Jbruslind/ECE341_Blue-1-/Junior Design Documentation/Review Presentation/Presentation Questions.docx

Presentation Questions

1. There are many options in regards to microcontrollers. What microcontrollers would perform best for low cost, bluetooth applications?
2. What are some options for electrical insulation for a product using 120V AC 60Hz power?
3. What are some common capabilities of “Smart” plugs?
