Jbruslind/ECE341_Blue-1-/Block Diagram/ECE341_Blue1_Block_Diagrams.docx

outside_to_system_acpwr

► system_to_outside_acpwr

Remote Switch

outside_to_system_usrin

► system_to_outside_usrout

outside_to_system_acpwr Fuse fused_acpwr Voltage

sensor_to_mcu_asig Sensor

mcu_dcpwr

sensor_to_mcu_dsig_1

system_to_outside_acpwr_1

ESP32

Block Owner

Smartphone App

Zach

Transformer

Voltage Sensor

Mack

Transformer

Jorian

ESP32

Mack

Fuse

Zach

Node

Jorian

²

_rwpcd_edonNode

Node

system_to_outside_acpwr_2

mcu_to_node_dsig_1

node_dcpwr_1

sensor_to_mcu_dsig_2

user_bluetooth_in

user_bluetooth_out

Smartphone App

user_wifi_out

²

_gisd_edon_ot_ucmuser_wifi_in

system_to_outside_usrout

outside_to_system_usrin

system_to_outside_ACpwr

sensor_to_mcu_ds

Node_dcpwr

Node "n"

C-13 AC

Plug

sensor_to_plug_fused_acpwr

mcu_to_node_dsig

relay_to_sensor_fused_acpwr

Power Relay

Current Sensor

fuse_acpwr

Interface Definitions

Interface Properties

outside_to_sytem_acpwr ● Vnominal: 120VAC via a NEMA 5-15R connector

● Ipeak: 15A

● Inominal: 500mA

fused_acpwr ● Vnominal: 120VAC via a NEMA 5-15R connector

● Ipeak: 5A

● Inominal: 500mA

● Disconnects system from input when 5A draw is exceeded

mcu_dcpwr ● Vnominal: 5VDC

● Inominal: 500mA

● Powers ESP32 Microcontroller

node_dcpwr_(n)* ● Vnominal: 5VDC

● Inominal: 500mA

● Powers Realys

sensor_to_mcu_dsig_(n)* ● Vnominal: <1VDC

● Reports current on output channels

● Inominal: <5A

mcu_to_node_dsig_(n)* ● Disables output after a time of upto 1 hour ± 1 minute when enabled

● Operate output channels independently

● Imax: 1.2A

user_bluetooth_in ● Enable/disable each channel

● Set delay on each output

● Interface must be via a mobile phone (Android)

user_bluetooth_out ● Display status of outputs

● Able to update output statuses from 20 feet away

user_wifi_in ● User interacts with system via Smartphone App

● Enable/disable each channel

● Set timer on each output

user_wifi_out ● Display status of outputs

● Able to update output statuses from 20 feet away

● Confirms length of timers

system_to_outside_usrout ● Display status of outputs

● Able to update output statuses from 20 feet away

● Confirms timers if set

outside _to_system_usrin ● User interacts with system via Smartphone App

● 9/10 users able to operate switches in <10 seconds without any previous training or knowledge of the interface

● Enable/Disable each channel

● Set delay on each output

● Accepts inputs from 20 feet away

● Disables output after a time of upto 1 hour ± 1 minute when enabled

system_to_outside_acpwr_(n)* ● Turn off and on at least 2 independent household lamps with up to 100W

incandescent bulbs and report current watts delivered by each channel

● Vnominal: 120VAC via a NEMA 5-15R connector

● Ipeak: 5A

● Inominal: 500mA

● Outputs will turn off after times of up to 60 minutes when selected

*note: n represents the nth redundant node
