Jbruslind/ECE341_Blue-1-/Final System Checkoff Documentation/Signature_Page.pdf

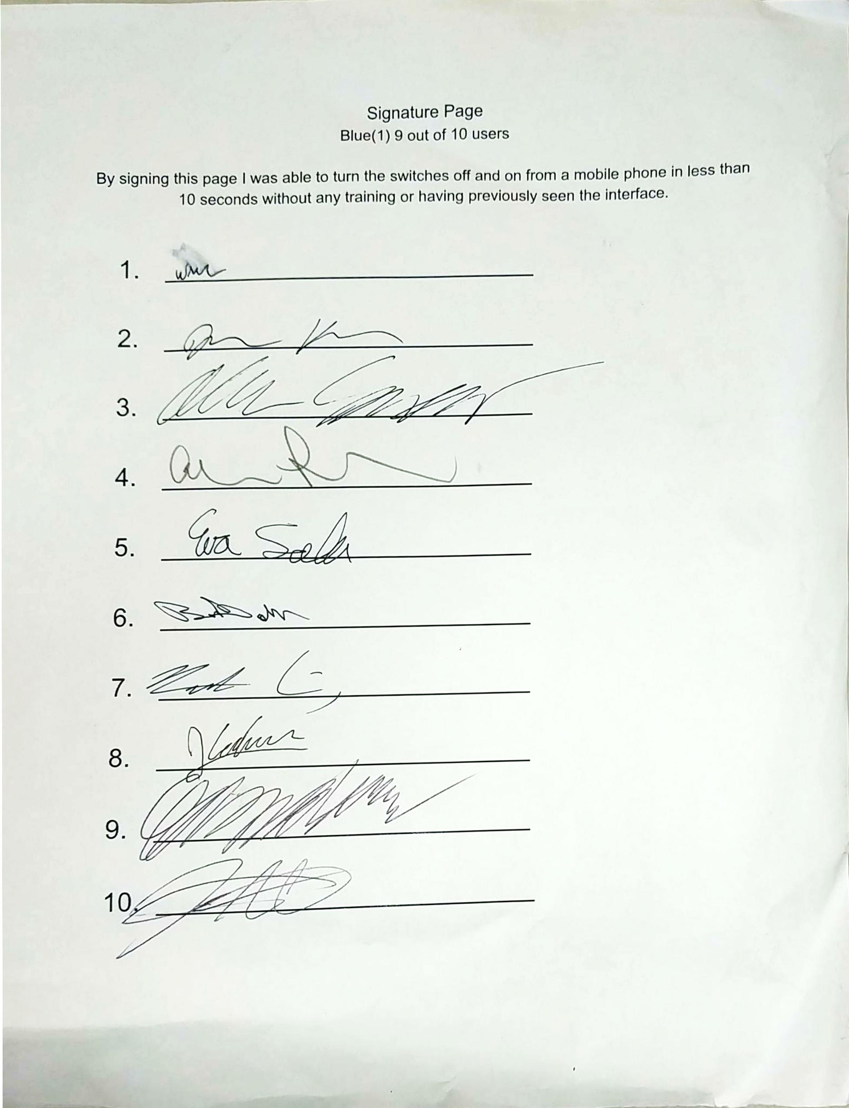
[picture p64: page 1]
