Jbruslind/ECE341_Blue-1-/Final System Checkoff Documentation/Black_Box.pdf

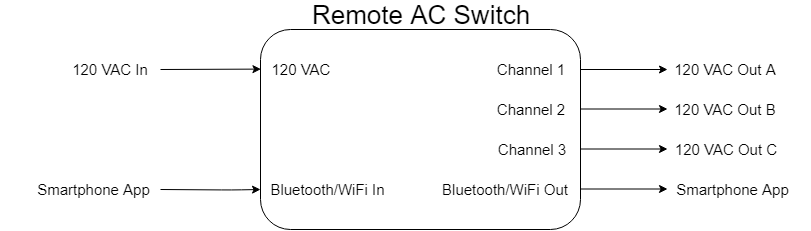
[picture p65: page 1]
