Jbruslind/ECE341_Blue-1-/Block Diagram/Old Versions/BlackBox.pdf

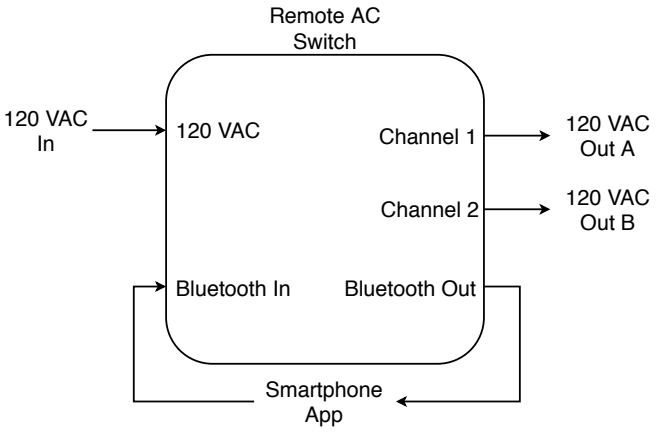
[picture p66: figure]
Remote AC Switch; 120 VAC In; 120 VAC Out A; Smartphone App; Channel 1; Channel 2; Bluetooth In; Bluetooth Out; 120 VAC; 120 VAC Out B
