Jbruslind/ECE341_Blue-1-/Block Diagram/Node_Internal.png

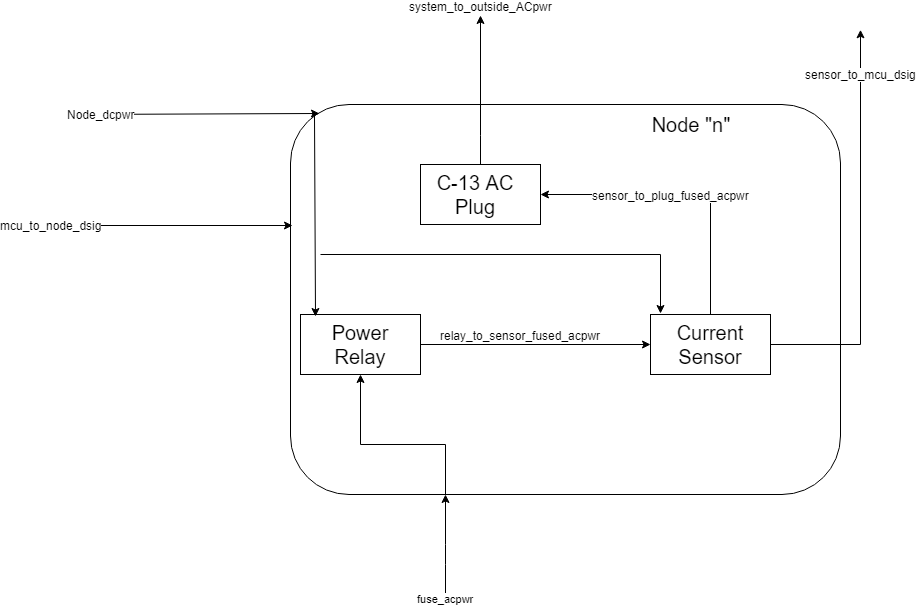
Block Diagram/Node_Internal.png
