Jbruslind/ECE341_Blue-1-/Junior Design Documentation/Poster/App Screen Shot.JPG

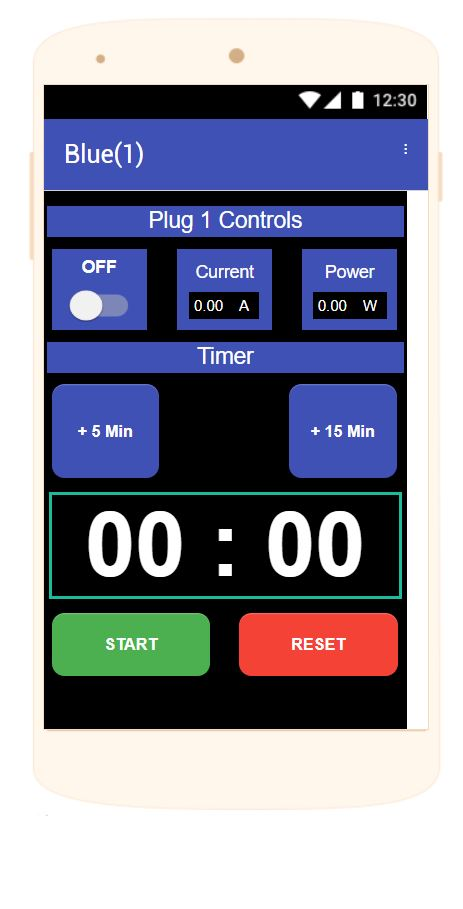
Junior Design Documentation/Poster/App Screen Shot.JPG
