Jbruslind/ECE341_Blue-1-/Junior Design Documentation/Poster/Team_photo.jpg

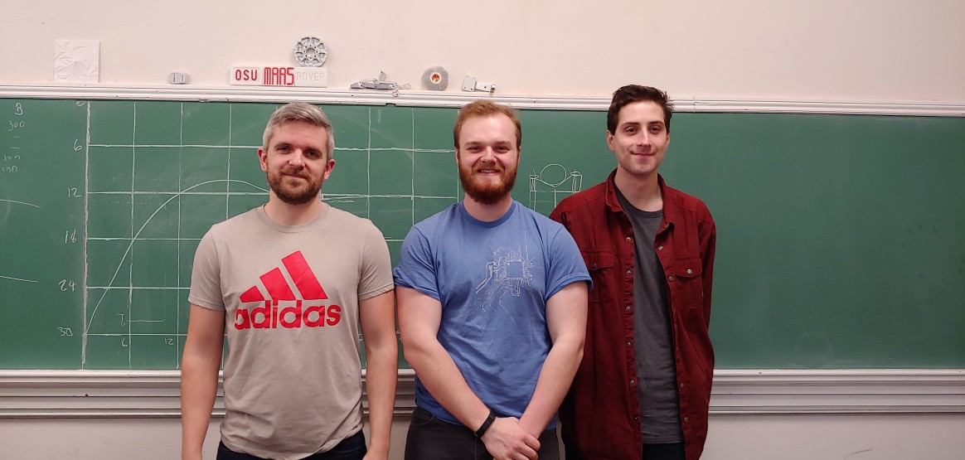
Junior Design Documentation/Poster/Team_photo.jpg
