Jbruslind/ECE341_Blue-1-/Readme_images/ACS71020_Current_Sense.png

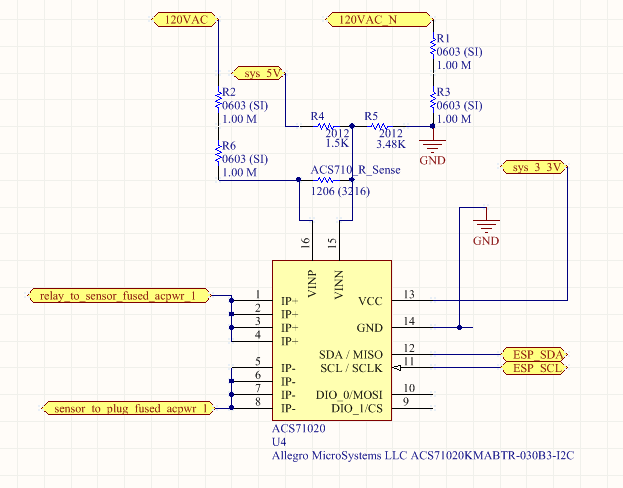
Readme_images/ACS71020_Current_Sense.png
