Jbruslind/ECE341_Blue-1-/Readme_images/Aylmao.jpg

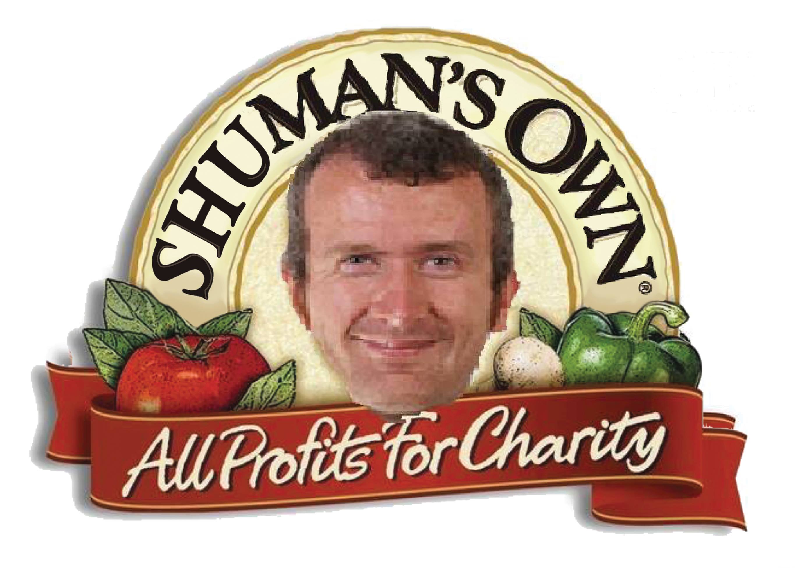
Readme_images/Aylmao.jpg
