Jbruslind/ECE341_Blue-1-/Readme_images/Output_Plugs.png

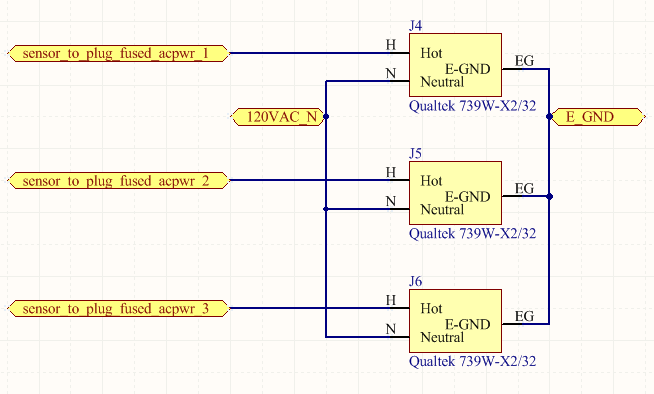
Readme_images/Output_Plugs.png
