Jbruslind/ECE341_Blue-1-/Readme_images/Status_LED.png

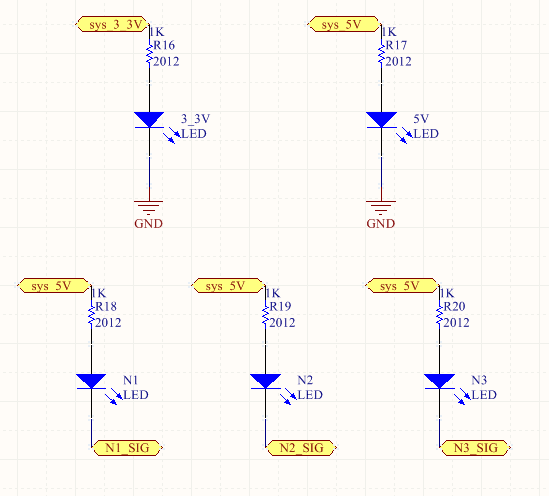
Readme_images/Status_LED.png
