Jbruslind/ECE341_Blue-1-/Case/Renders/2019-02-07 13_01_42-Autodesk Inventor Professional 2019 - [Assembly99.iam].png

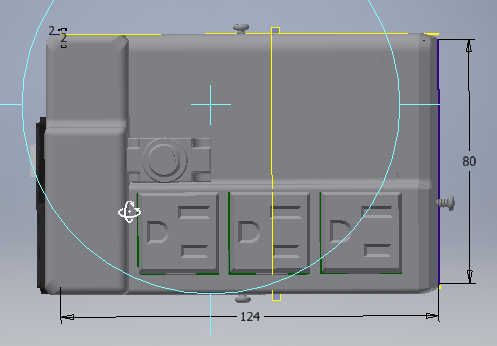
Case/Renders/2019-02-07 13_01_42-Autodesk Inventor Professional 2019 - [Assembly99.iam].png
