Jbruslind/ECE341_Blue-1-/Schematics/Schematic Files/Input Plugs.pdf

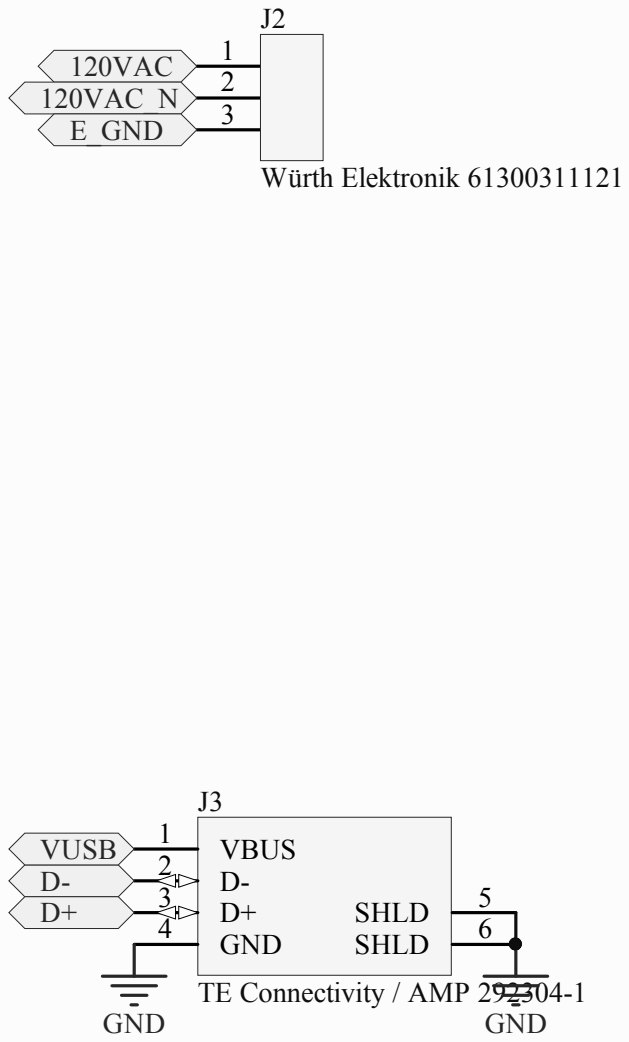
[picture p101: page 1]
Title; Size; Number; Revision; Date:; Sheet of; File:; Input_Plugs.SchDoc; Drawn By:; Würth Elektronik 61300311121; 120VAC 120VAC_N E_GND; VBUS 1 D- 2 D+ 3; GND 4; SHLD; VUSB; GND; PIJ201; PIJ202 PIJ203; COJ2; PIJ301 PIJ302 PIJ303 PIJ304; PIJ305 PIJ306; COJ3; PO120VACPIJ201 PO120VAC0NPIJ202; POD0PIJ303; POD0PIJ302; POE0GNDPIJ203; PIJ304; POVUSBPIJ301; PO120VAC PO120VAC0N; POD0; POE0GND

TE Connectivity / AMP 292304-1
