Jbruslind/ECE341_Blue-1-/Schematics/Schematic Files/Transformer.pdf

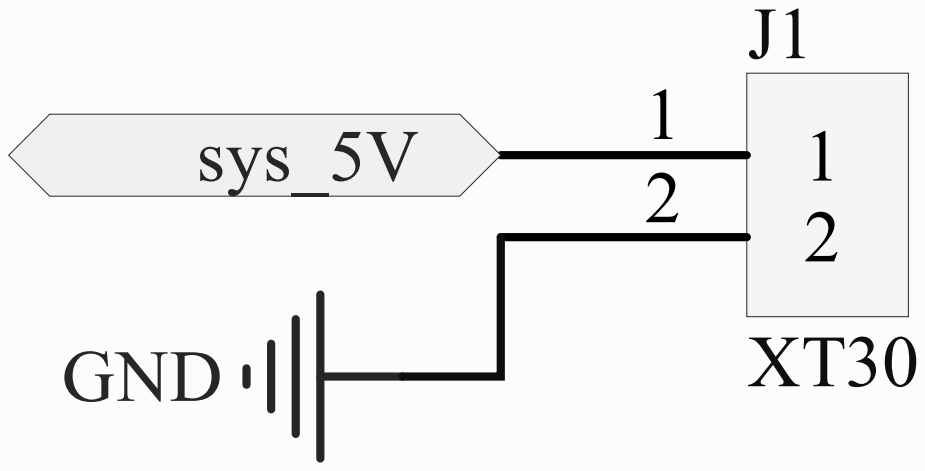
[picture p102: page 1]
Title; Size; Number; Revision; Date:; Sheet of; File:; Transformer.SchDoc; Drawn By:; GND; sys_5V PIJ101; PIJ102; COJ1; POsys05V POSYS05V
