Jbruslind/ECE341_Blue-1-/Block Diagram/HighLevelBlockDiagramV3.pdf

# Case

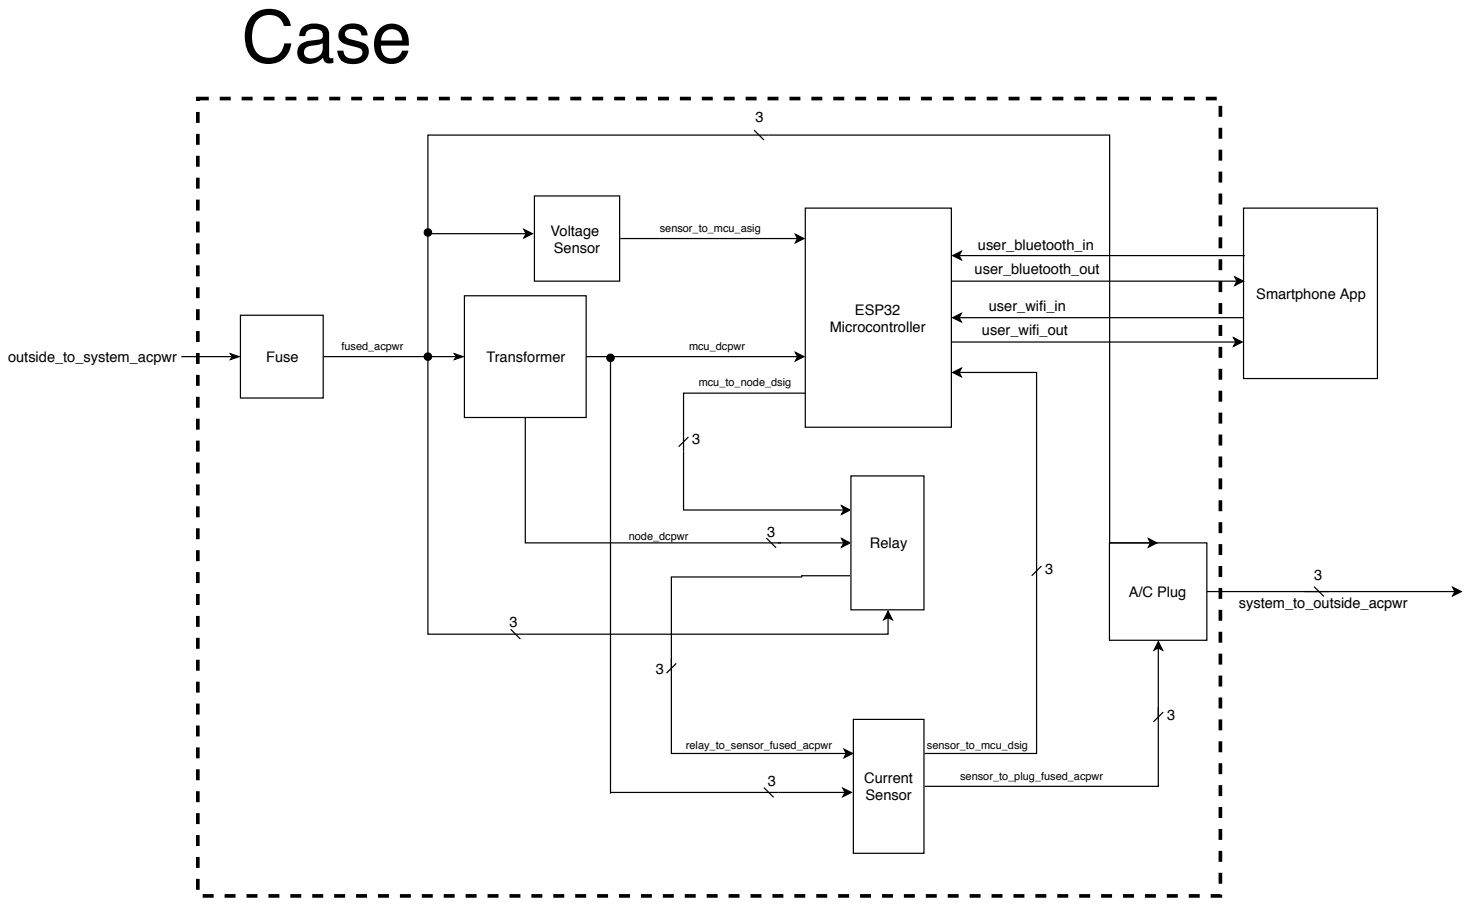
[picture p103: page 1]
A/C Plug; Fuse; Transformer; Voltage Sensor; fused_acpwr; outside_to_system_acpwr; Smartphone App; mcu_dcpwr; sensor_to_mcu_asig; ESP32 Microcontroller; Current Sensor; Relay; relay_to_sensor_fused_acpwr; node_dcpwr; system_to_outside_acpwr; mcu_to_node_dsig; sensor_to_plug_fused_acpwr; sensor_to_mcu_dsig; user_bluetooth_in; user_bluetooth_out; user_wifi_out; user_wifi_in
