Jbruslind/ECE341_Blue-1-/PCB Production Files/MK1.0/Bluetooth Switch/Bluetooth Switch.PDF

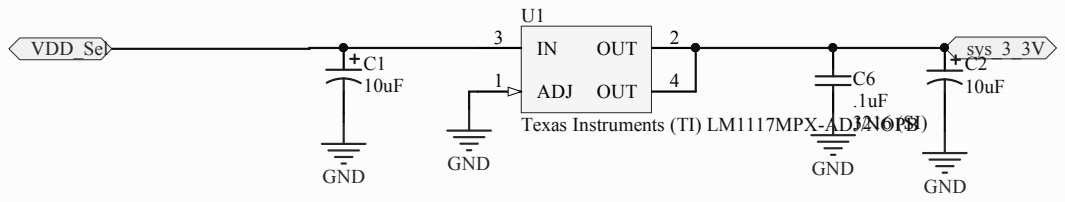
[picture p104: page 1]
s Ins; sys_3_3V C1

Date:; Sheet of; File:; Current_Sensors_ACS.SchDoc; Drawn By:

File:; Current_Voltage_Sensor_ACS.SchDoc; Drawn By:; DIO_1/CS; 9 DIO_0/MOSI; SCL / SCLK; 11 SDA / MISO; VINN 15; VINP 16; Allegro MicroSystems LLC ACS71020KMABTR-030B3-I2C

File:; Fuse.SchDoc; Drawn By:; PO120VAC0Unreg PO120VAC0UNREG; PO120VAC

File:; Input_Plugs.SchDoc; Drawn By:; FCI 10103592-0001LF; Würth Elektronik 61300311121


File:; Output_Plugs.SchDoc; Drawn By:; Hot H; Neutral N; E-GND; Qualtek 739W-X2/32


MBT2222ADW1T1G

D3 1N4148 | COIL- 2

File:; Status_LEDs.SchDoc; Drawn By:

File:; Transformer.SchDoc; Drawn By:; Pololu XT60 YELLOW; POsys05V POSYS05V

File:; UART_Bridge.SchDoc; Drawn By:; VDD 6; REGIN 7; VBUS 8; RST 9; SUSPEND; 11 SUSPEND; RXD; 25 TXD; DSR; 27 DTR

Silicon Labs CP2102-GM

File:; Voltage_Selector.SchDoc; Drawn By:; 4 GND 2; VDD 1; Maxim Integrated MAX40200AUK+T; PID401; POVDD0Sel PID403

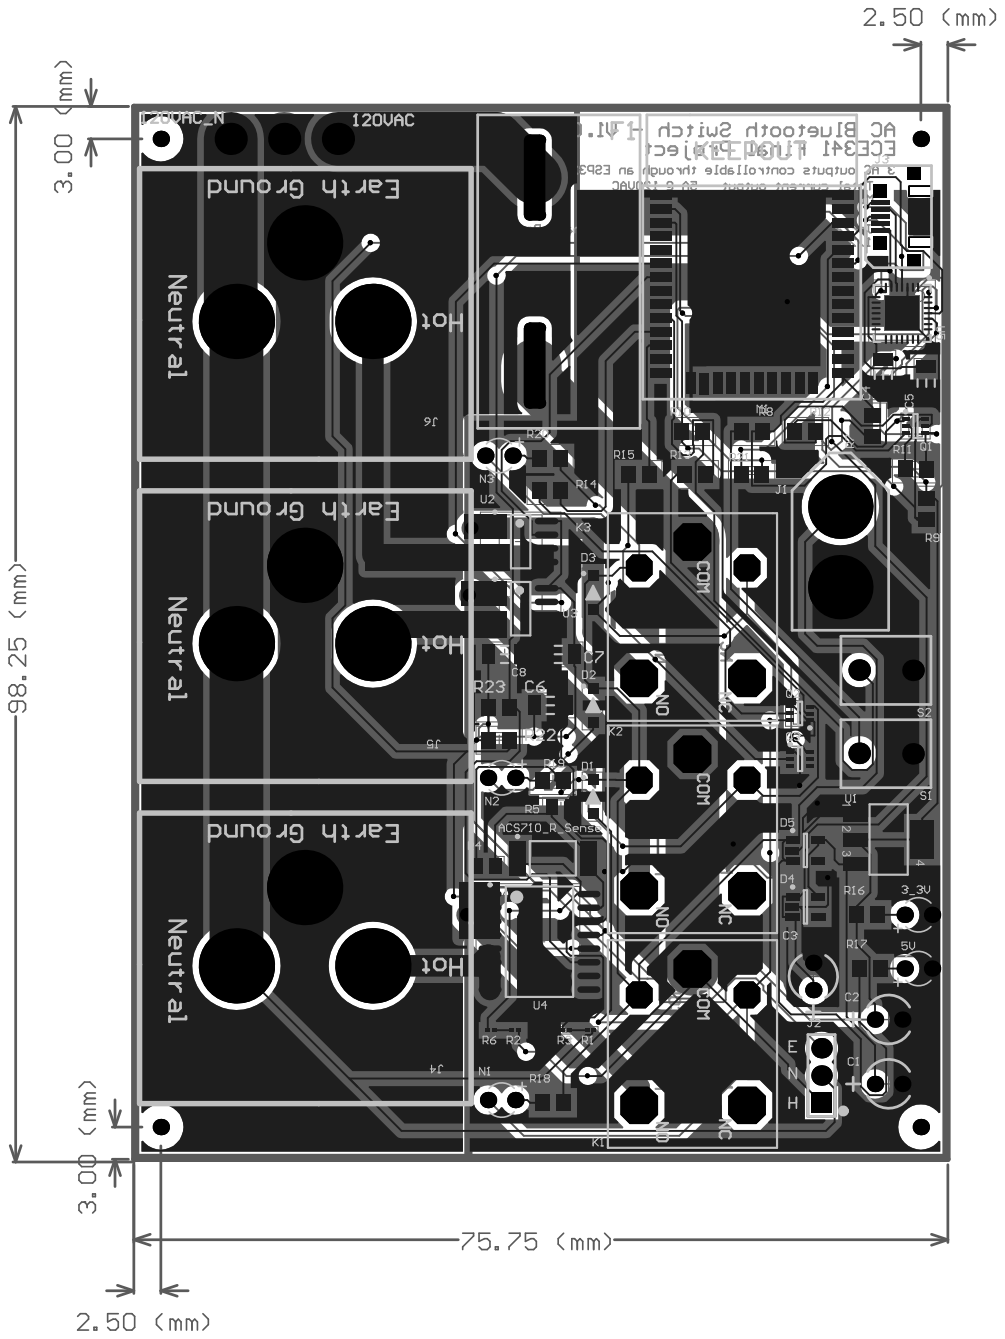
[picture p105: page 13]
