Jbruslind/ECE341_Blue-1-/PCB Production Files/MK1.1/Bluetooth Switch/Bluetooth Switch.PDF

s Ins; sys_3_3V C1

Date:; Sheet of; File:; Current_Sensors_ACS.SchDoc; Drawn By:

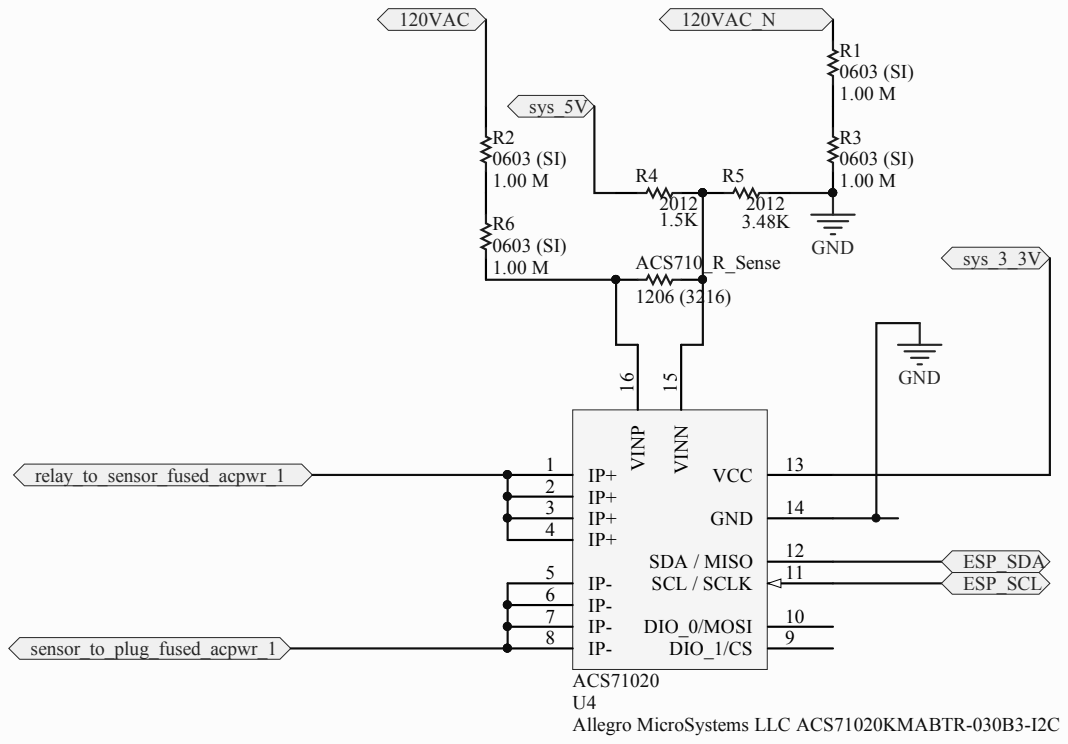
[picture p106: page 3]
File:; Current_Voltage_Sensor_ACS.SchDoc; Drawn By:; DIO_1/CS; 9 DIO_0/MOSI; SCL / SCLK; 11 SDA / MISO; VINN 15; VINP 16; Allegro MicroSystems LLC ACS71020KMABTR-030B3-I2C

File:; Fuse.SchDoc; Drawn By:; PO120VAC0Unreg PO120VAC0UNREG; PO120VAC

File:; Input_Plugs.SchDoc; Drawn By:; Würth Elektronik 61300311121; VBUS 1 D- 2 D+ 3; GND 4; SHLD

TE Connectivity / AMP 292304-1

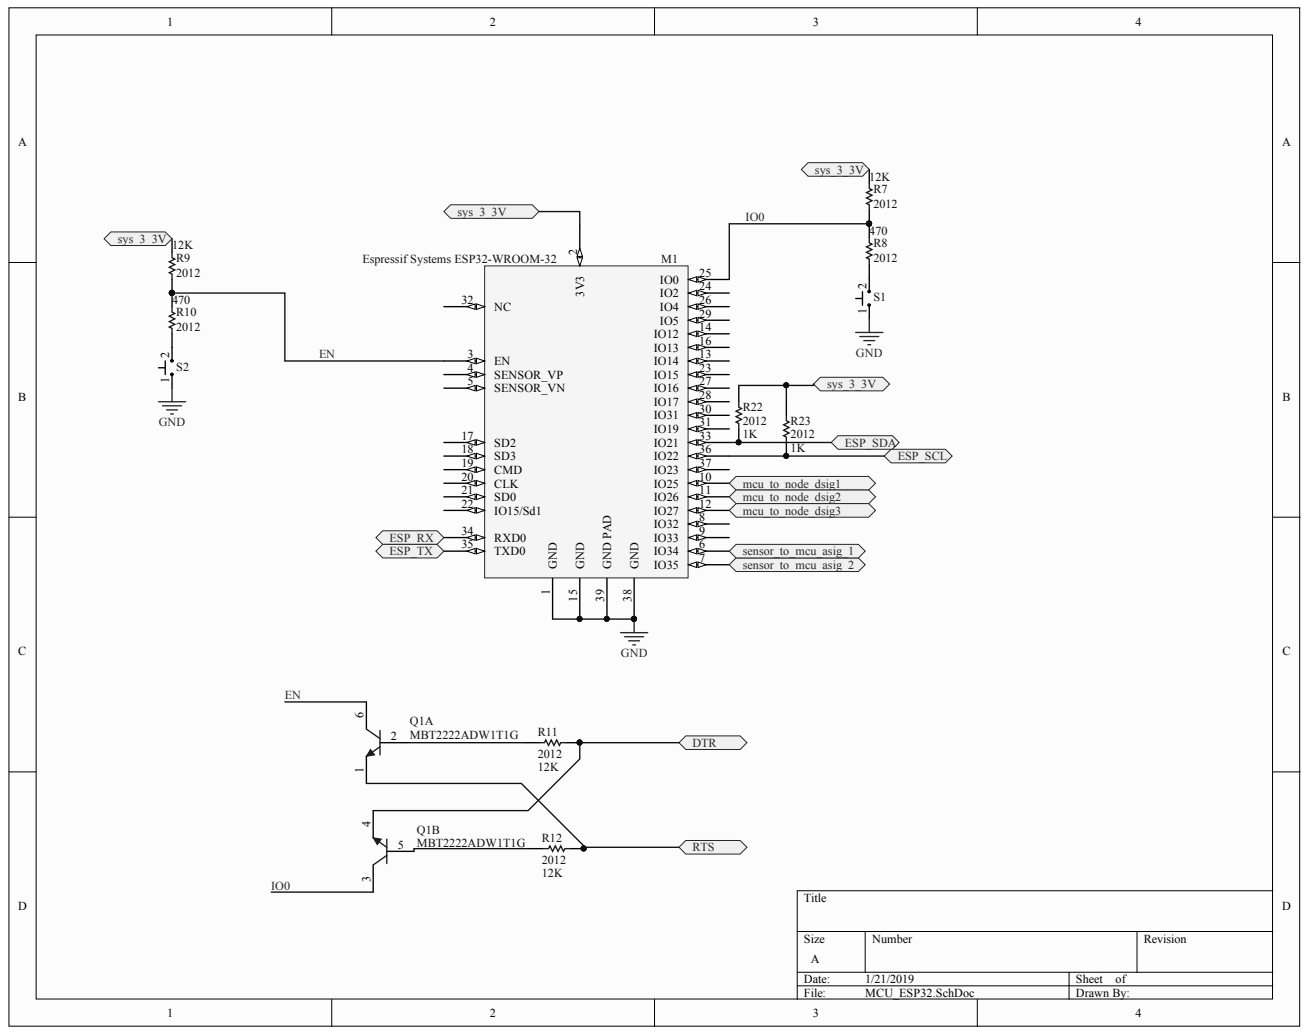
[picture p107: page 6]

File:; Output_Plugs.SchDoc; Drawn By:; Hot H; Neutral N; E-GND; Qualtek 739W-X2/32

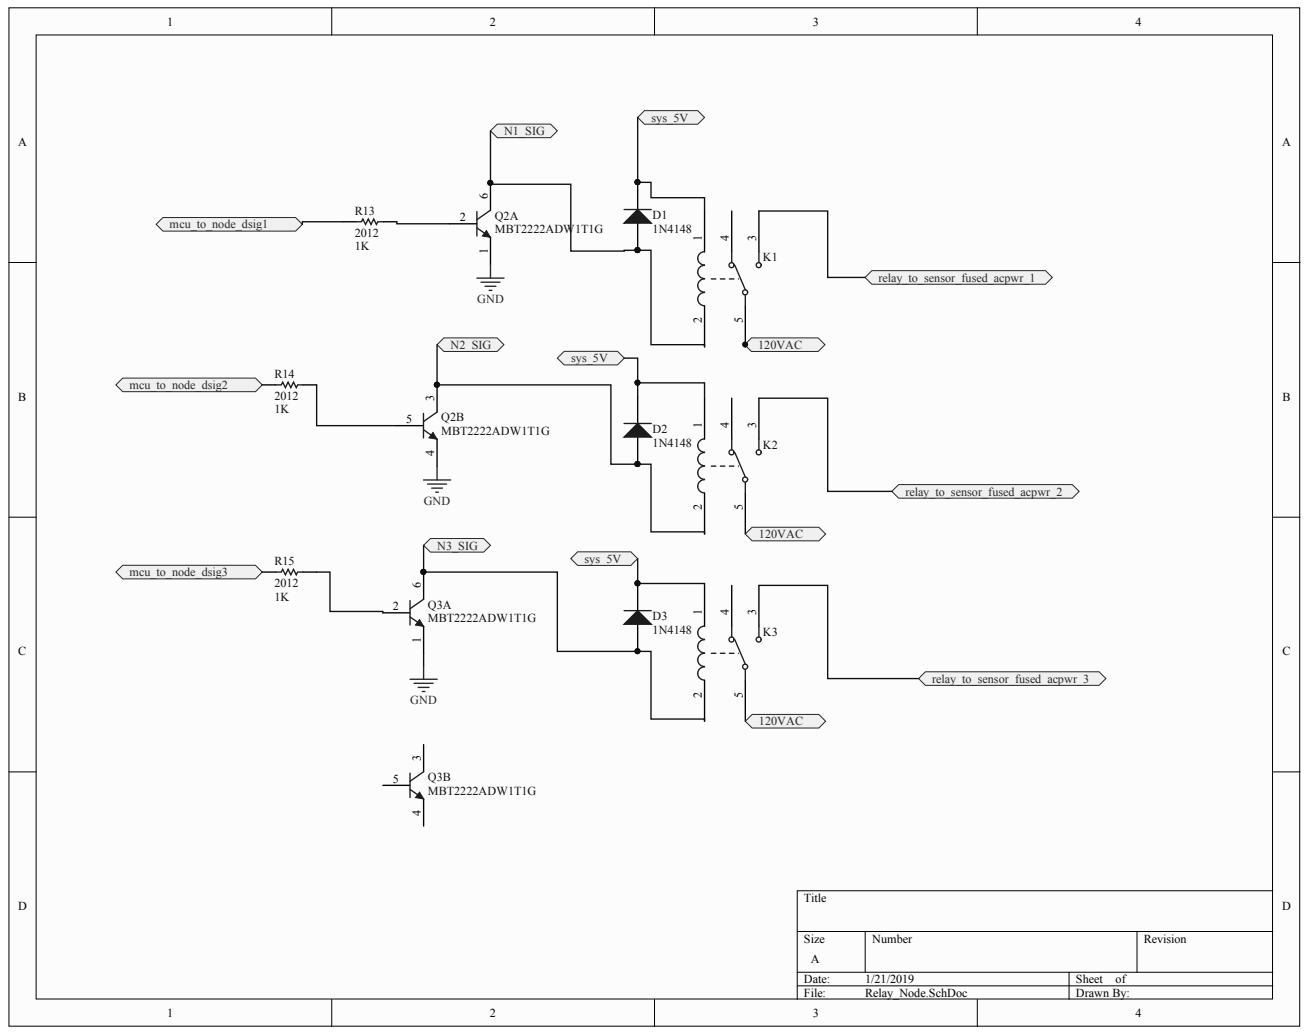
[picture p108: page 8]

File:; Status_LEDs.SchDoc; Drawn By:

File:; Transformer.SchDoc; Drawn By:; sys_5V PIJ101; POsys05V POSYS05V

File:; UART_Bridge.SchDoc; Drawn By:; VDD 6; REGIN 7; VBUS 8; RST 9; SUSPEND; 11 SUSPEND; RXD; 25 TXD; DSR; 27 DTR

Silicon Labs CP2102-GM

File:; Voltage_Selector.SchDoc; Drawn By:; 4 GND 2; VDD 1; Maxim Integrated MAX40200AUK+T; PID401; POVDD0Sel PID403

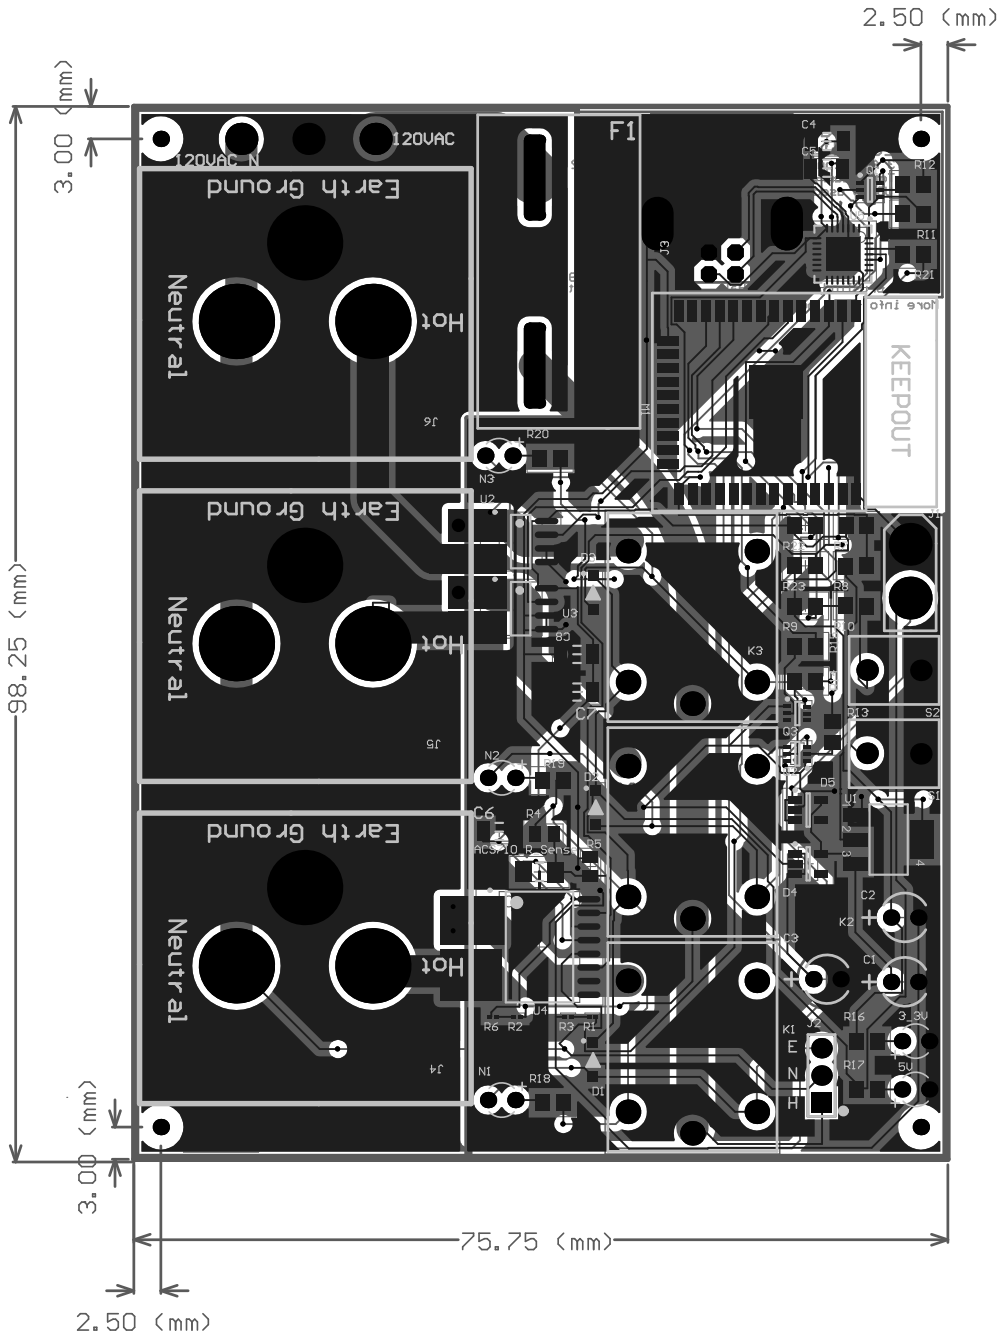
[picture p109: page 13]
