Jbruslind/ECE341_Blue-1-/Case/Back_View.pdf

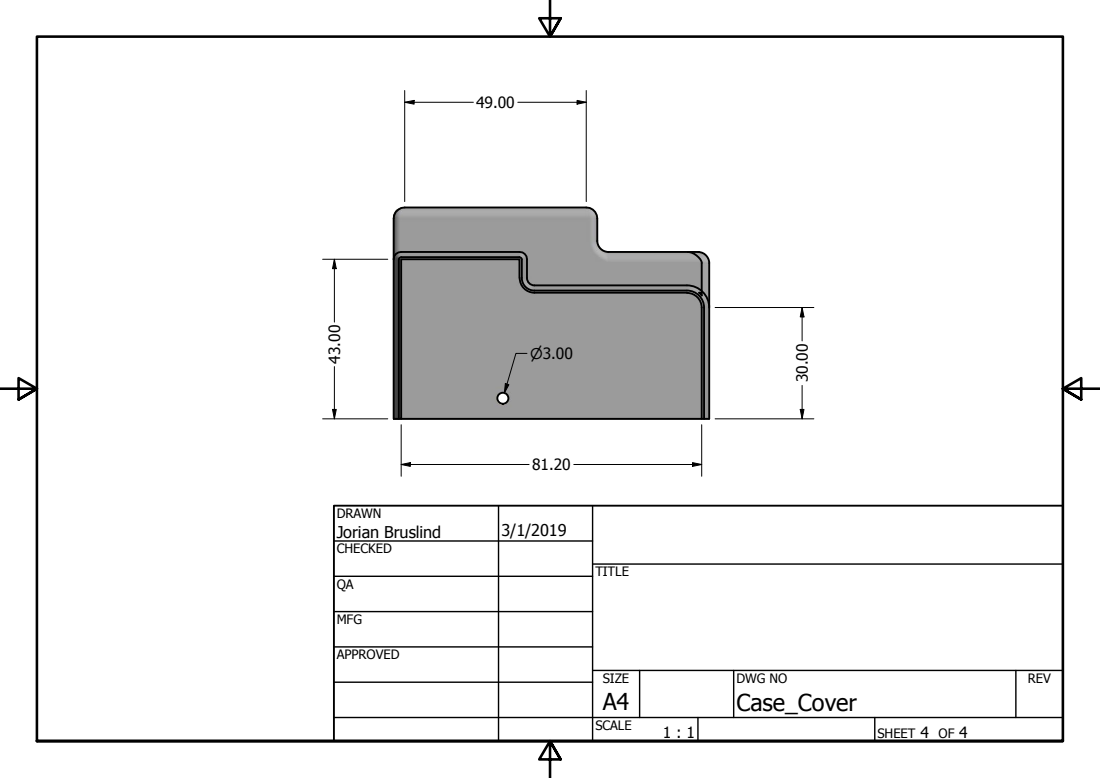
[picture p110: page 1]

DRAWN Jorian Bruslind | 3/1/2019

CHECKED

MFG

APPROVED

SIZE A4 | DWG NO Case_Cover | REV

SCALE 1 : 1 | | SHEET 4 OF 4
