Jbruslind/ECE341_Blue-1-/Case/Case_Top_Front.pdf

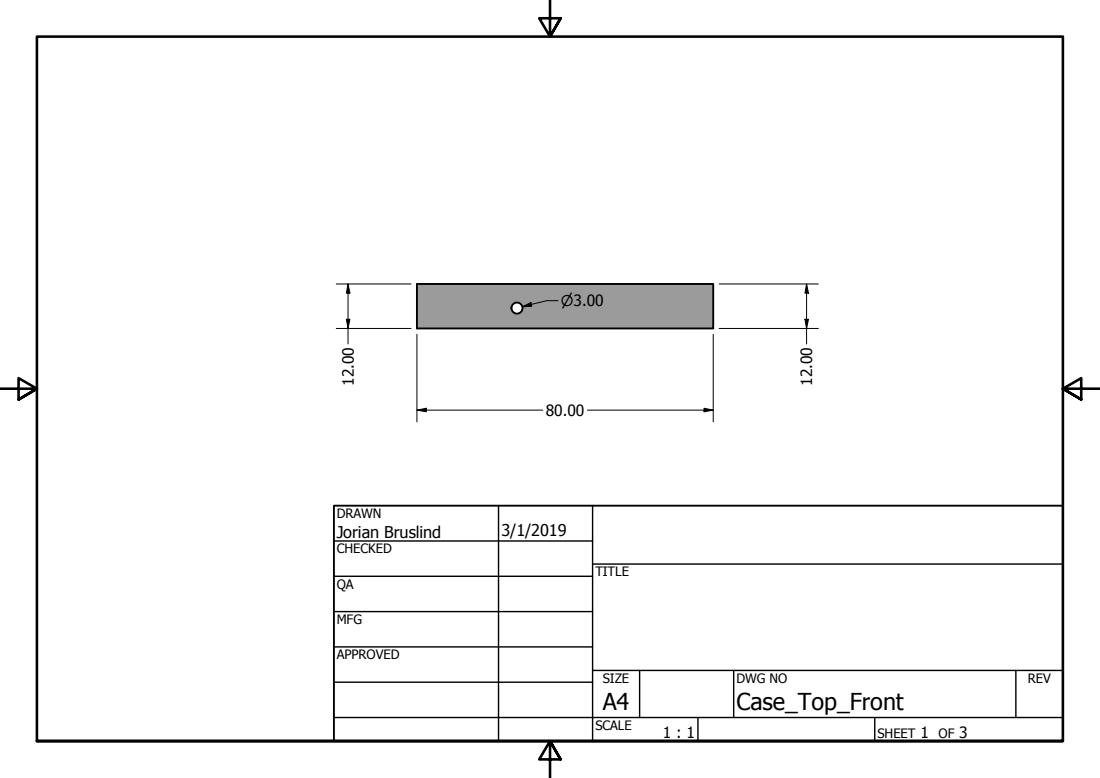
[picture p111: page 1]

DRAWN Jorian Bruslind | 3/1/2019

CHECKED

MFG

APPROVED

SIZE A4 | DWG NO Case_Top_Front | REV

SCALE 1 : 1 | | SHEET 1 OF 3
