Jbruslind/ECE341_Blue-1-/Final System Checkoff Documentation/Case_Drawings.pdf

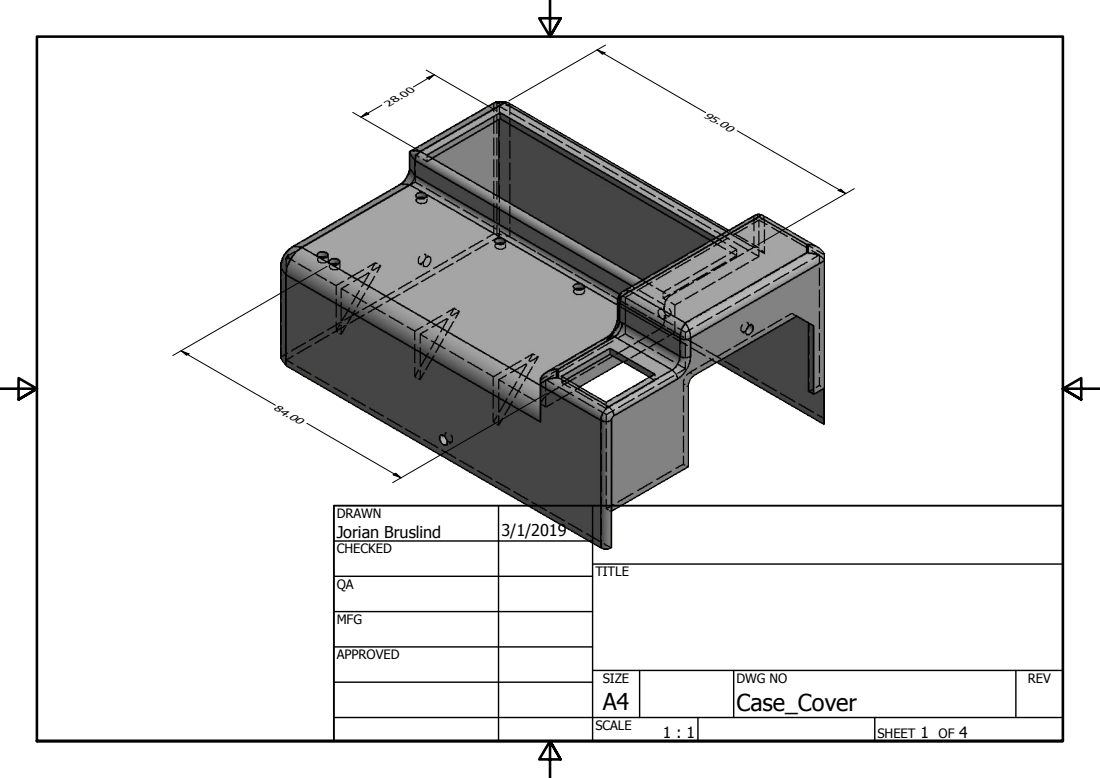
[picture p112: page 1]
SHEET 1 OF 4; DRAWN; CHECKED; MFG; APPROVED; Jorian Bruslind; DWG NO Case_Cover; TITLE; SIZE A4; SCALE; REV

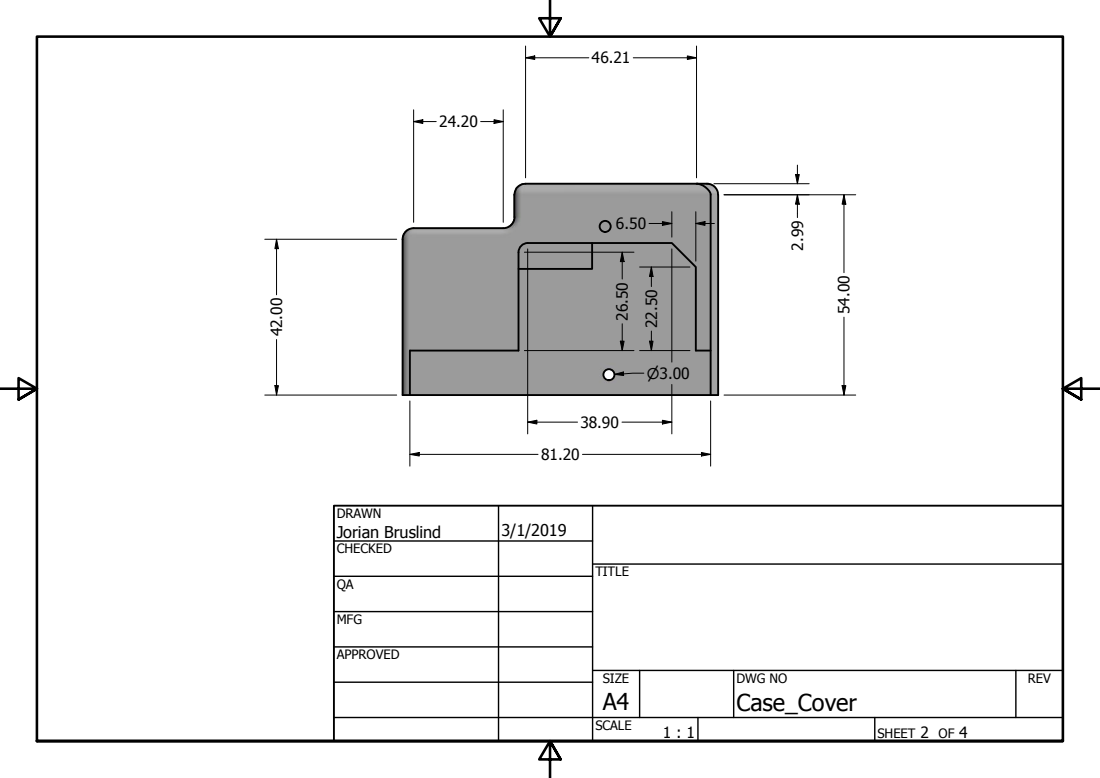
[picture p113: page 2]
DRAWN; CHECKED; MFG; APPROVED; Jorian Bruslind; DWG NO Case_Cover; TITLE; SIZE A4; REV

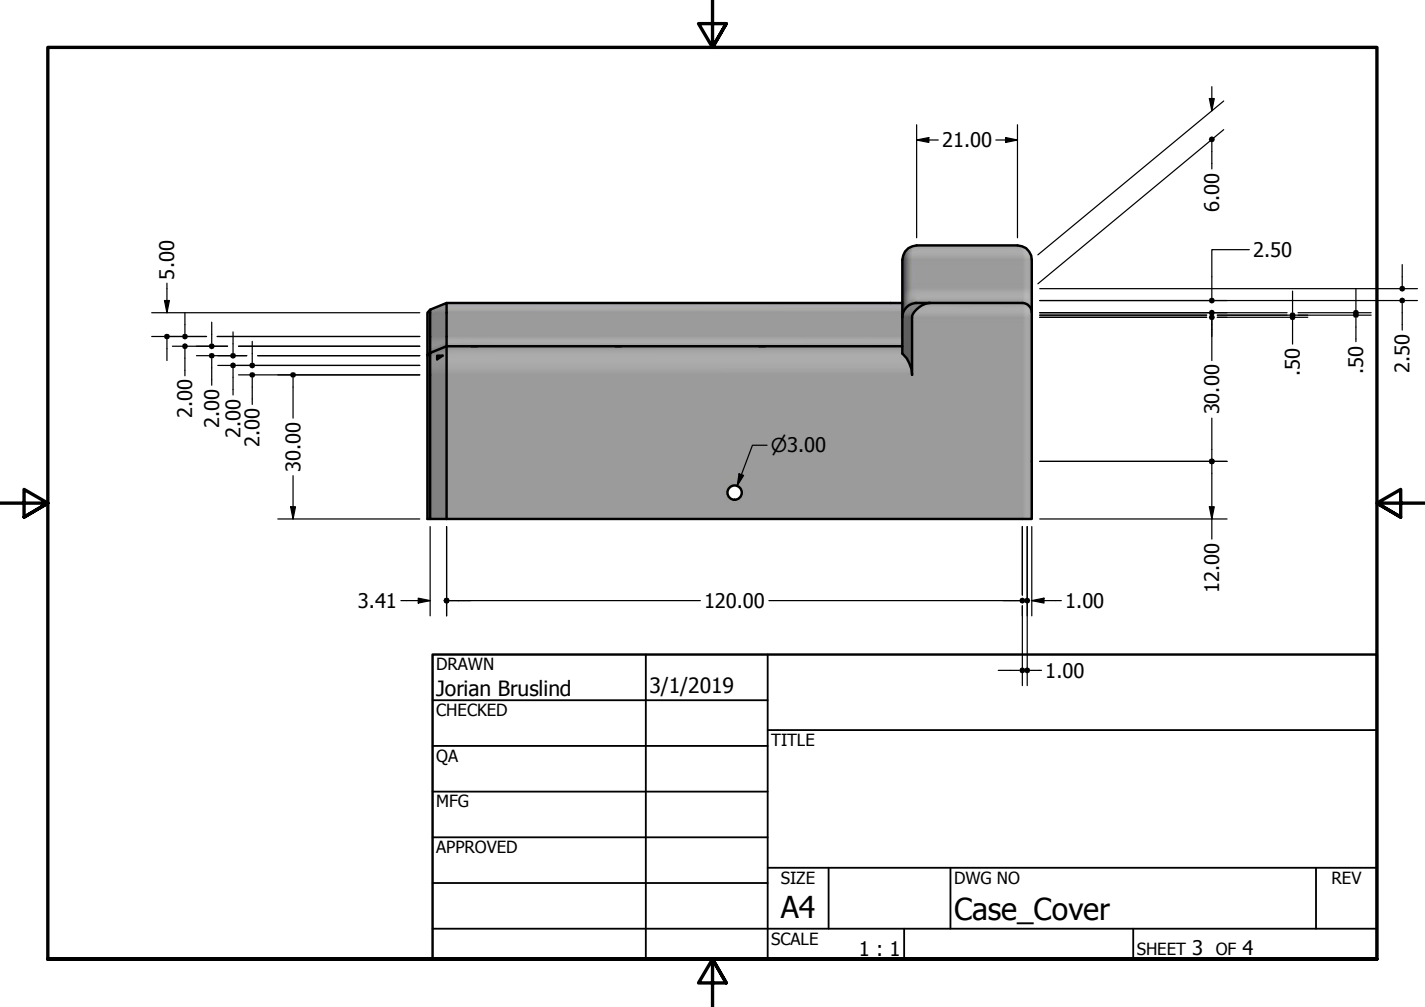
[picture p114: page 3]
DRAWN; CHECKED; MFG; APPROVED; Jorian Bruslind; DWG NO Case_Cover; TITLE; SIZE A4; REV

DRAWN; CHECKED; MFG; APPROVED; Jorian Bruslind; DWG NO Case_Cover; TITLE; SIZE A4; REV

DRAWN; CHECKED; MFG; APPROVED; Jorian Bruslind; DWG NO Case_Top_Front; TITLE; SIZE A4; REV

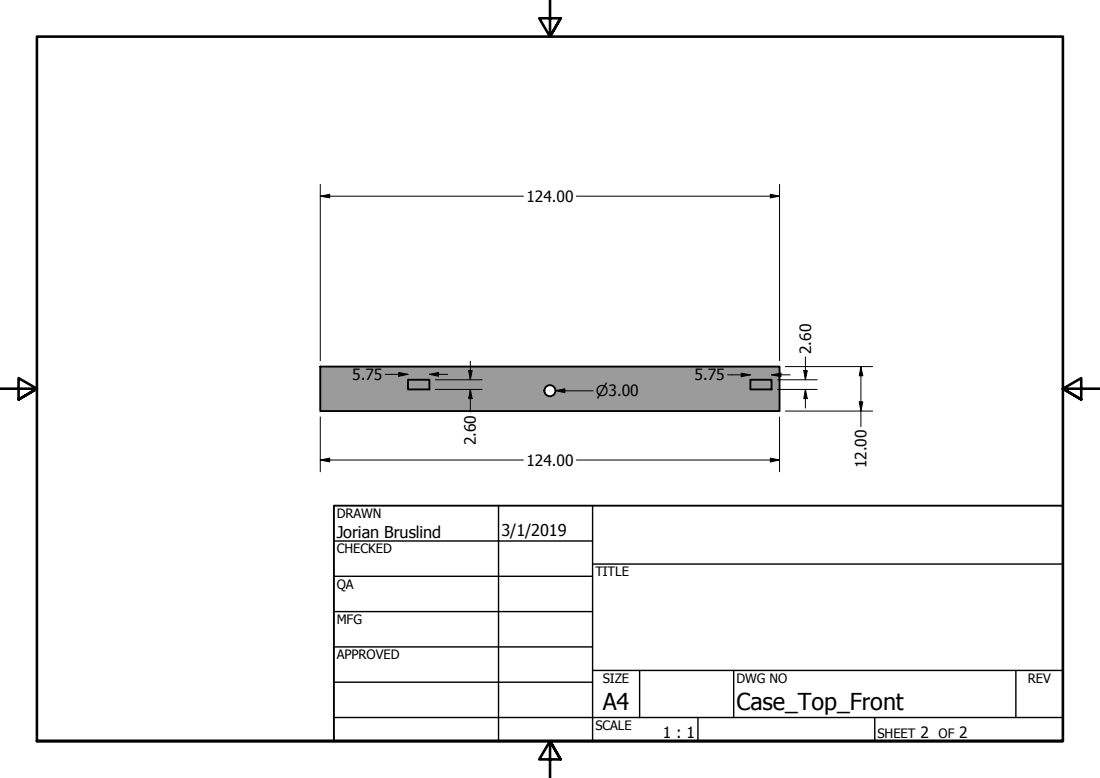
[picture p115: page 6]
DRAWN; CHECKED; MFG; APPROVED; Jorian Bruslind; DWG NO Case_Top_Front; TITLE; SIZE A4; REV

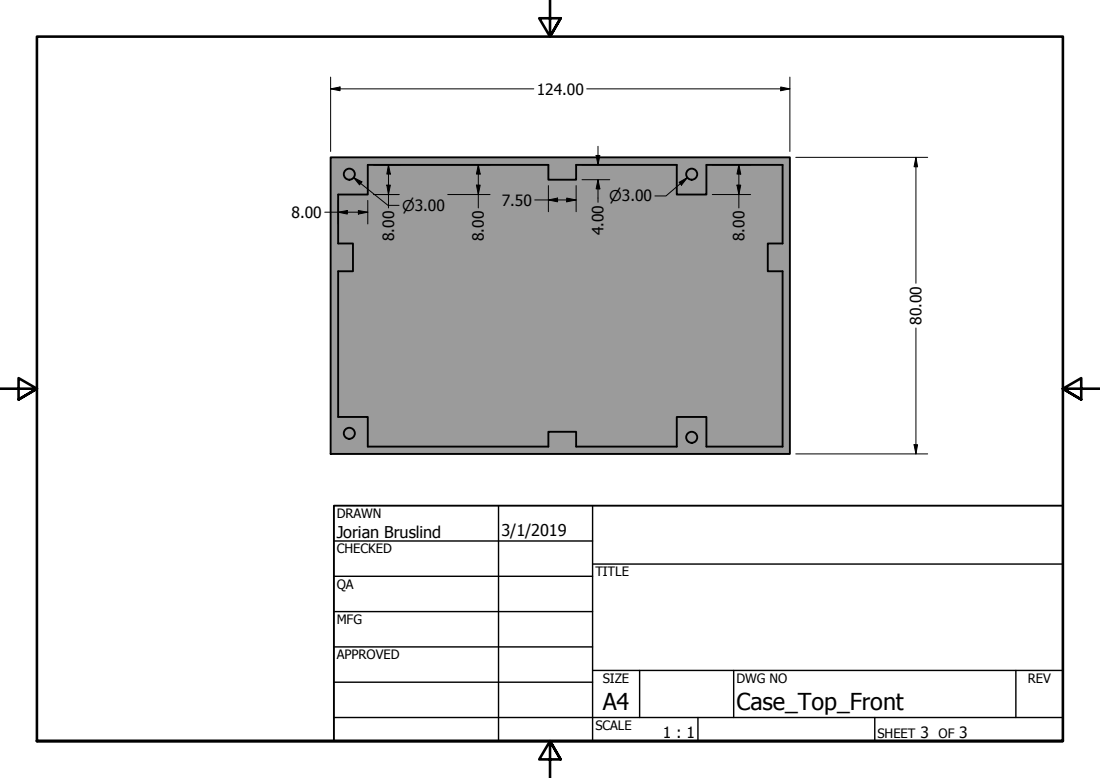
[picture p116: page 7]
DRAWN; CHECKED; MFG; APPROVED; Jorian Bruslind; DWG NO Case_Top_Front; TITLE; SIZE A4; REV
