Jbruslind/ECE341_Blue-1-/Final System Checkoff Documentation/PCB_Layers.pdf

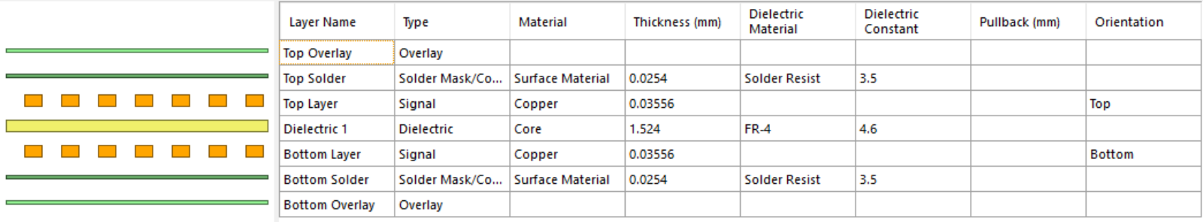
[picture p117: page 1]
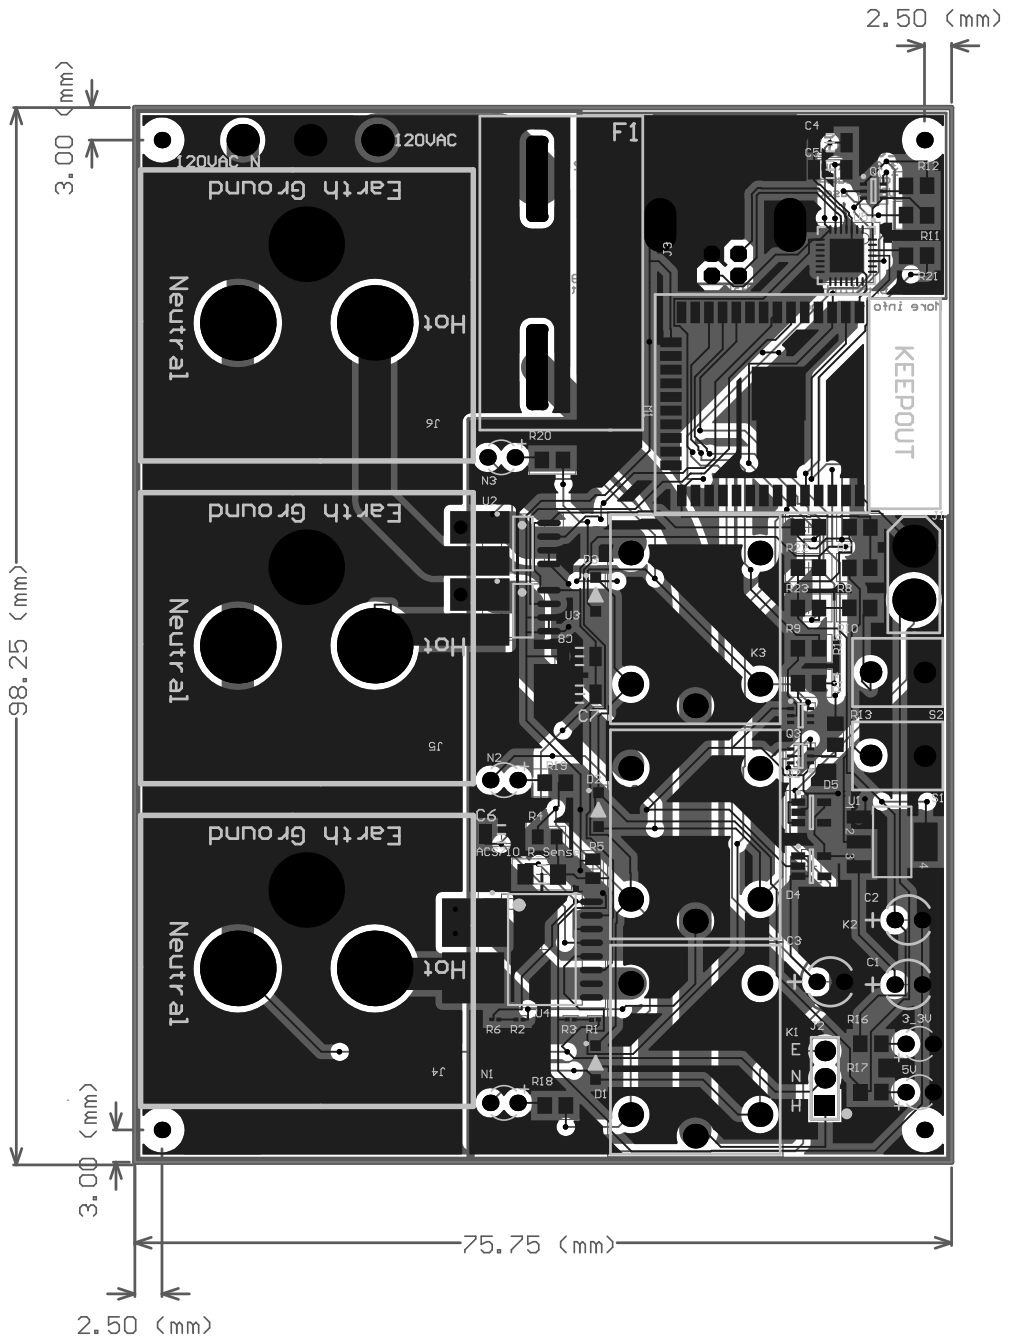
[picture p118: page 2]

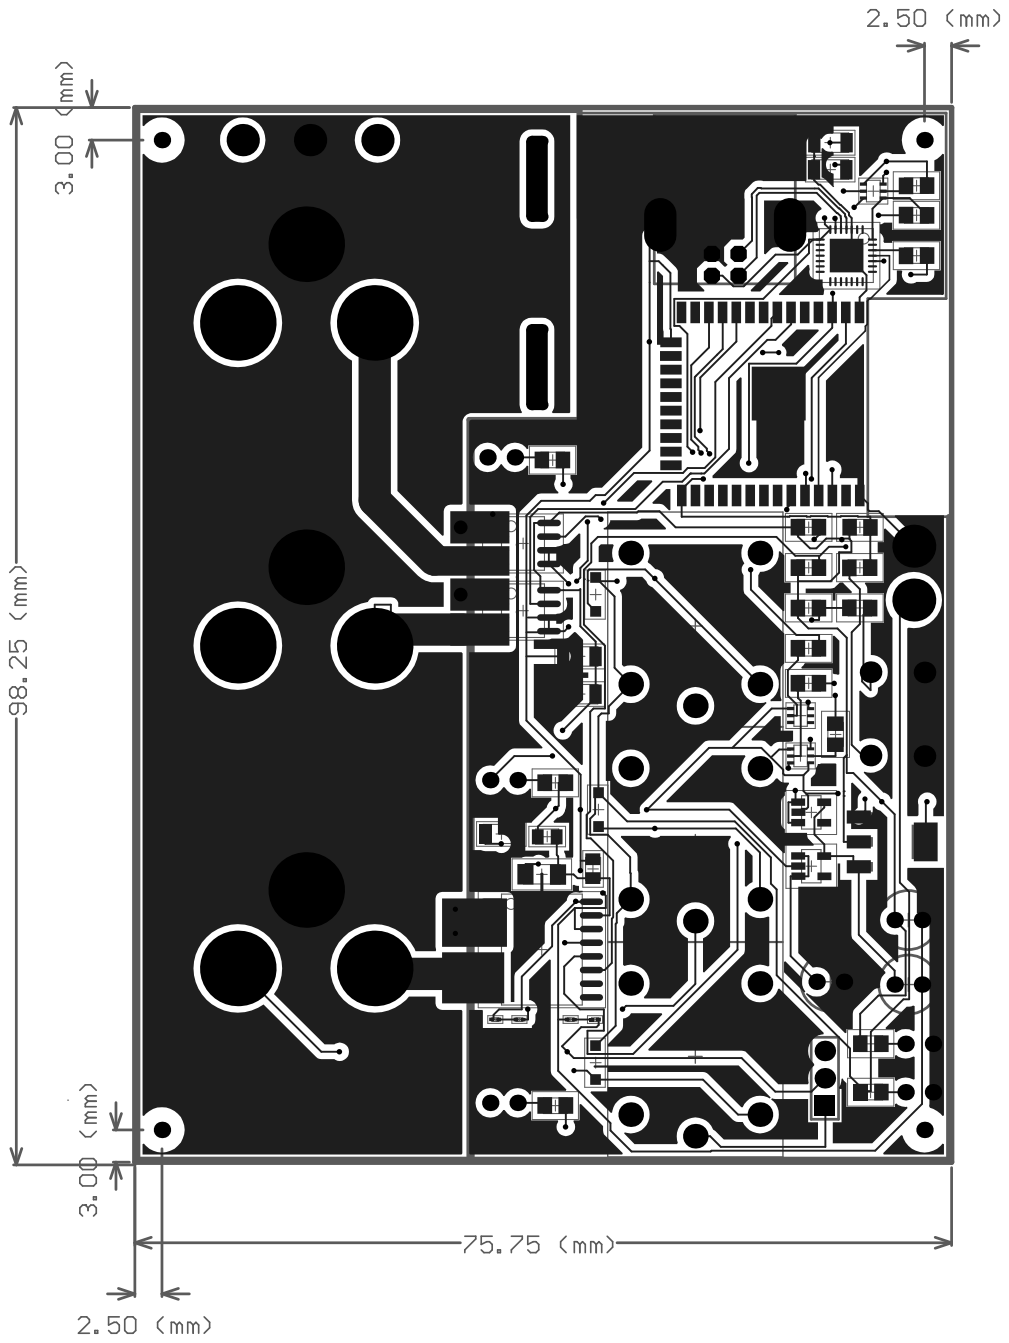
[picture p119: page 3]

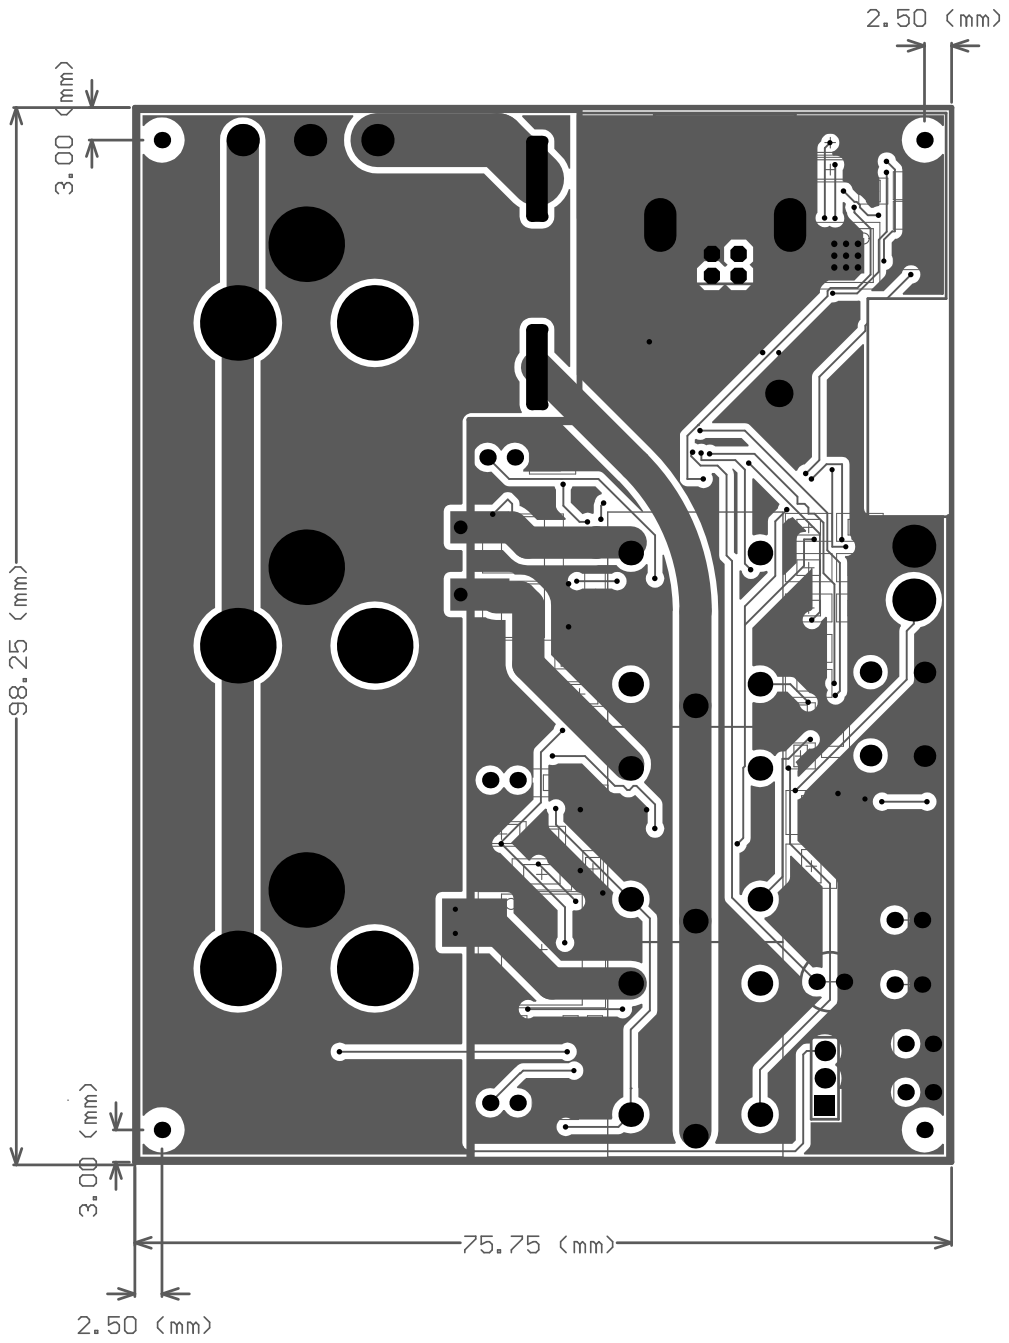
[picture p120: page 4]

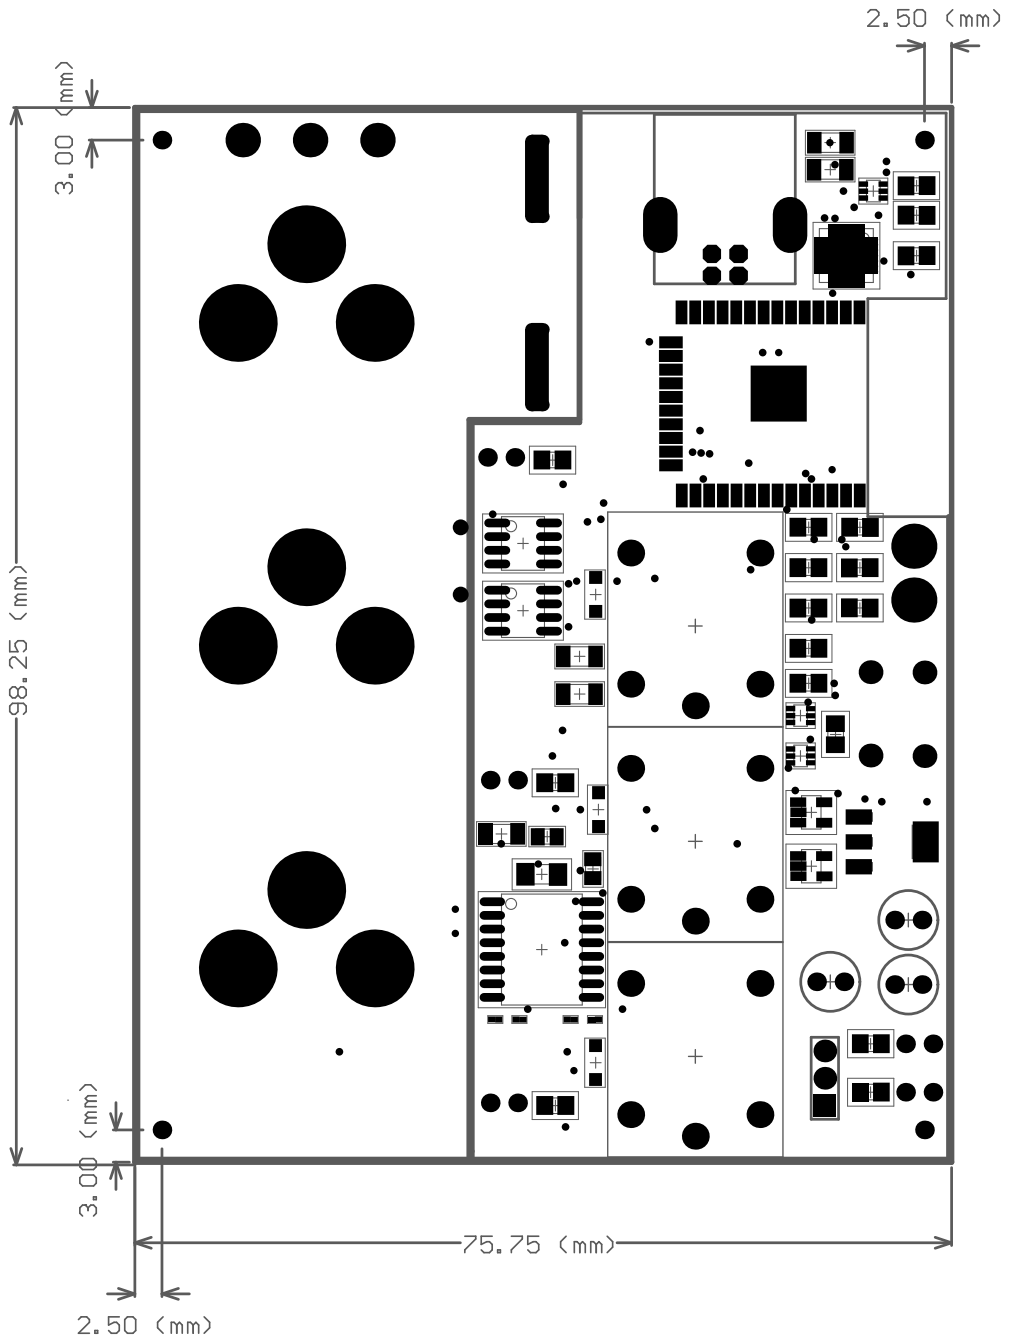
[picture p121: page 5]

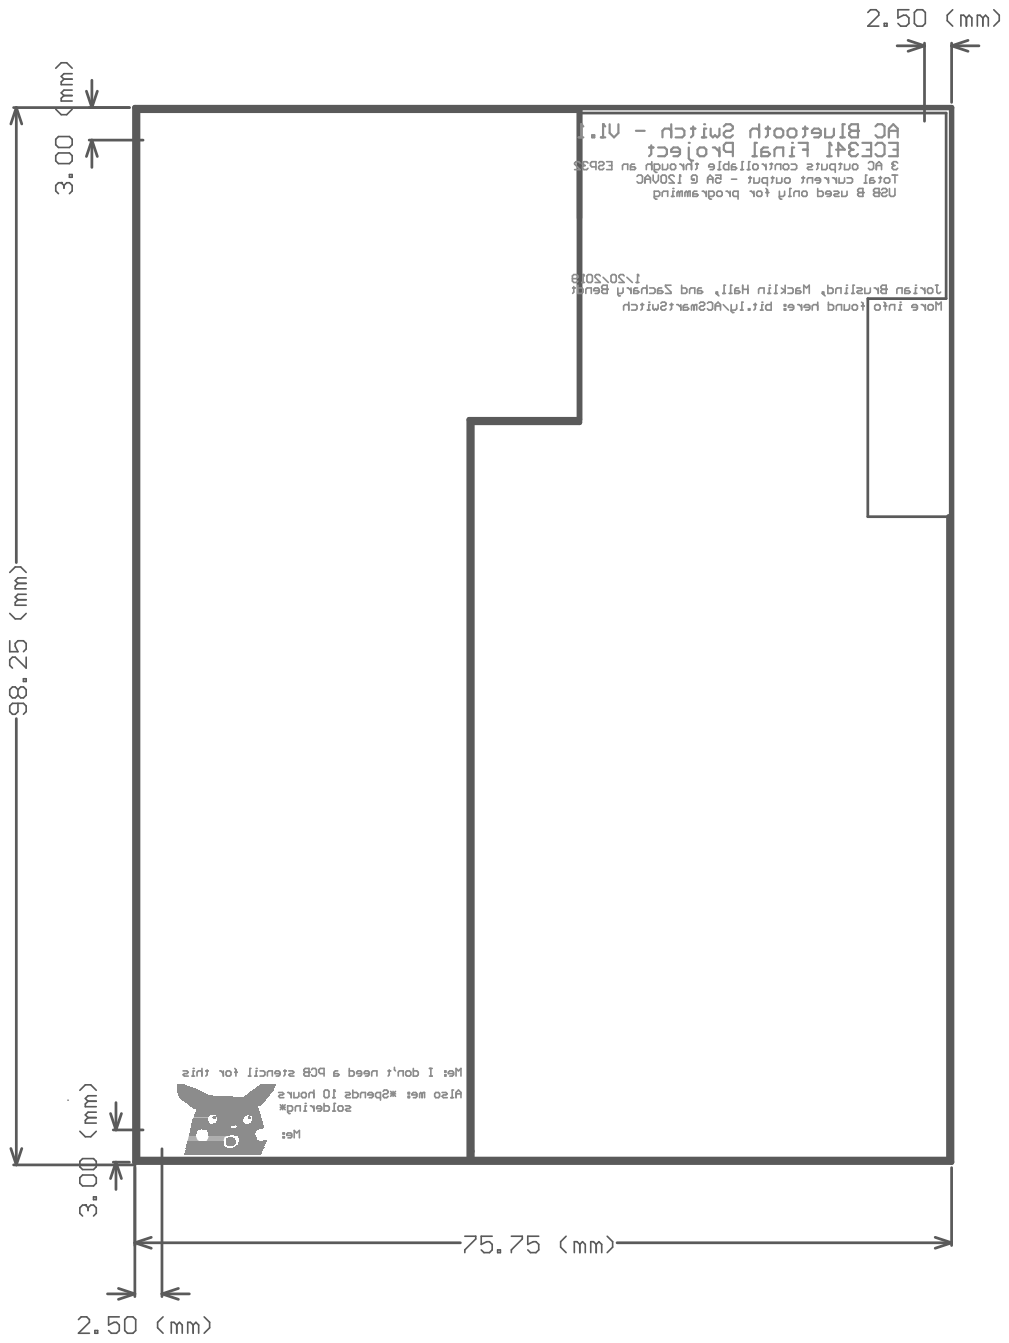
[picture p122: page 6]
