Jbruslind/ECE341_Blue-1-/Block Diagram/Old Versions/HighLevelBlockDiagram(1).pdf

# Remote AC Switch

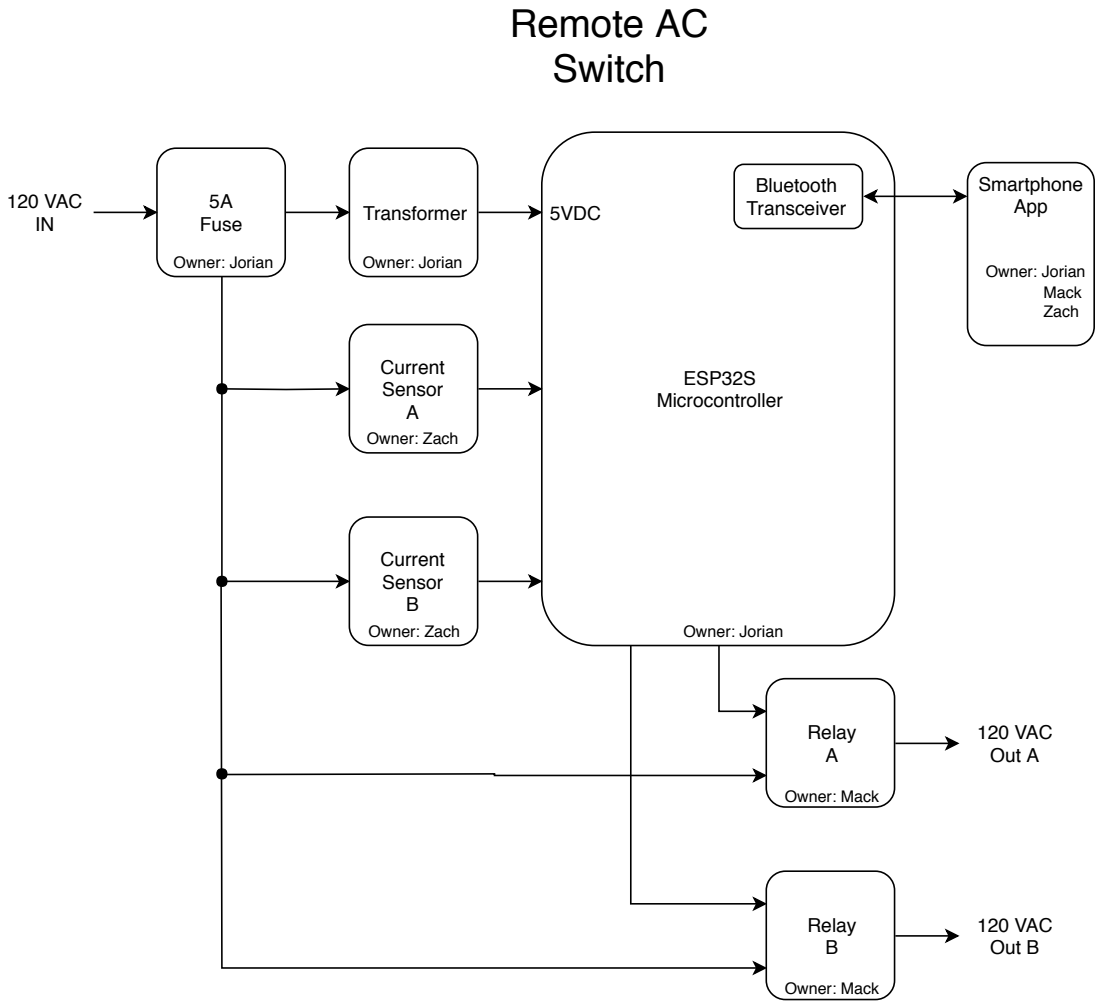
[picture p123: page 1]
120 VAC IN; 5A Fuse; ESP32S Microcontroller; Transformer; Current Sensor A; Relay A; Relay B; Current Sensor B; 5VDC; Bluetooth Transceiver; Smartphone App; Owner: Jorian; Owner: Zach; Owner: Jorian Mack Zach; Owner: Mack; 120 VAC Out A; 120 VAC Out B
