Jbruslind/ECE341_Blue-1-/Block Diagram/Old Versions/HighLevelBlockDiagram.pdf

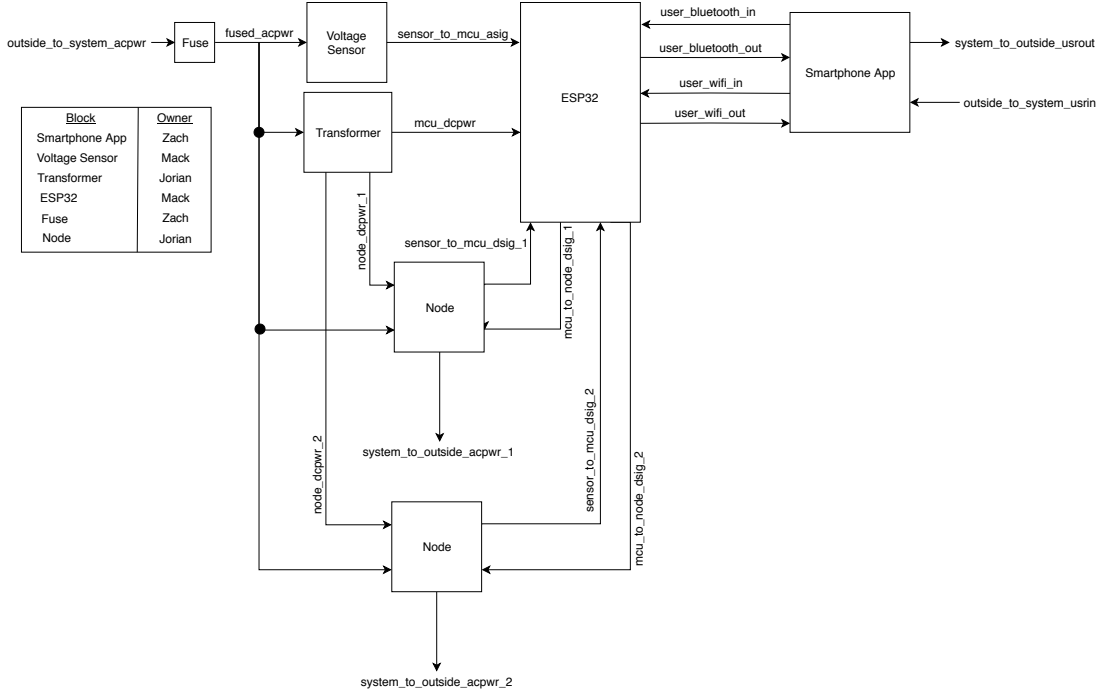
[picture p124: page 1]
outside_to_system_acpwr; Fuse; fused_acpwr; Voltage; Sensor; mcu_dcpwr; ESP32; Transformer; sensor_to_mcu_asig; sensor_to_mcu_dsig_1; system_to_outside_acpwr_1; user_wifi_in; user_bluetooth_in; Smartphone App; system_to_outside_usrout; outside_to_system_usrin; user_bluetooth_out; user_wifi_out; mcu_to_node_dsig_2; Block; Owner; Voltage Sensor; Node; Zach; Jorian; Mack; node_dcpwr_2; system_to_outside_acpwr_2 node_dcpwr_1; sensor_to_mcu_dsig_2; mcu_to_node_dsig_1
